vsirvent/Open-Synscan/SynScan/app/TickTimer.cpp

/*
 * This file is part of the Open Synscan Project distribution (https://github.com/vsirvent/Synscan).
 * Copyright (c) 2019 Vicente Sirvent Orts.
 *
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
 * You should have received a copy of the GNU General Public License
 * along with this program. If not, see <http://www.gnu.org/licenses/>.
 */

#include "TickTimer.h"

#define FRC1_ENABLE_TIMER  BIT7
#define FRC1_AUTO_LOAD  BIT6

TickTimer AppTimer;

//TIMER PREDIVED MODE
typedef enum {
	DIVDED_BY_1 = 0,		//timer clock
	DIVDED_BY_16 = 4,	//divided by 16
	DIVDED_BY_256 = 8,	//divided by 256
} TIMER_PREDIVED_MODE;

typedef enum {			//timer interrupt mode
	TM_LEVEL_INT = 1,	// level interrupt
	TM_EDGE_INT = 0,	//edge interrupt
} TIMER_INT_MODE;

typedef enum {
	FRC1_SOURCE = 0, NMI_SOURCE = 1,
} FRC1_TIMER_SOURCE_TYPE;

static void IRAM_ATTR tick_timer_isr_cb(void *arg)
{
	if (arg == null) {
		return;
	}
	((TickTimer*)arg)->onTick();
	return;
}

TickTimer::TickTimer() {
	ETS_FRC_TIMER1_INTR_ATTACH((void*)tick_timer_isr_cb, (void *) this);
}

TickTimer::~TickTimer() {
	ETS_FRC_TIMER1_INTR_ATTACH((void*)tick_timer_isr_cb, (void*)null);
	stop();
}

void IRAM_ATTR
TickTimer::onTick() {
	int size = mListener.size();
	for (int i = 0; i < size; ++i) {
		mListener[i]->onTick();
	}
}

bool TickTimer::start(bool repeating) {
	this->mRepeating = repeating;
	stop();
	if (mInternal == 0) {
		return mStarted;
	}

	if (this->mRepeating == 1) {
		RTC_REG_WRITE(FRC1_CTRL_ADDRESS,
		FRC1_AUTO_LOAD | DIVDED_BY_16 | FRC1_ENABLE_TIMER | TM_EDGE_INT);
	} else {
		RTC_REG_WRITE(FRC1_CTRL_ADDRESS,
				DIVDED_BY_16 | FRC1_ENABLE_TIMER | TM_EDGE_INT);
	}

	TM1_EDGE_INT_ENABLE();
	ETS_FRC1_INTR_ENABLE();
	mStarted = true;

	RTC_REG_WRITE(FRC1_LOAD_ADDRESS, mInternal);
	return mStarted;
}

bool TickTimer::stop() {
	if (!mStarted) {
		return mStarted;
	}
	TM1_EDGE_INT_DISABLE();
	ETS_FRC1_INTR_DISABLE();
	mStarted = false;
	return mStarted;
}

bool TickTimer::restart() {
	stop();
	start(mRepeating);
	return mStarted;
}

bool TickTimer::isStarted() {
	return mStarted;
}

uint32_t TickTimer::getIntervalTicks() const {
	return mInternal;
}

bool TickTimer::setIntervalTicks(uint32_t ticks) {
	if (ticks > 0) {
		mInternal = ticks;
		if (mStarted) {
			restart();
		}
	} else {
		stop();
	}
	return mStarted;
}

void TickTimer::addListener(ITickListener* listener) {
	ETS_INTR_LOCK();
	if (!mListener.contains(listener)) {
		mListener.add(listener);
	}
	ETS_INTR_UNLOCK();
}

void TickTimer::removeListener(ITickListener* listener) {
	ETS_INTR_LOCK();
	mListener.removeElement(listener);
	ETS_INTR_UNLOCK();
}
